fabianhartmann2/Deployment-Tower/exports/step/coupon_wifi_dock_v2.step

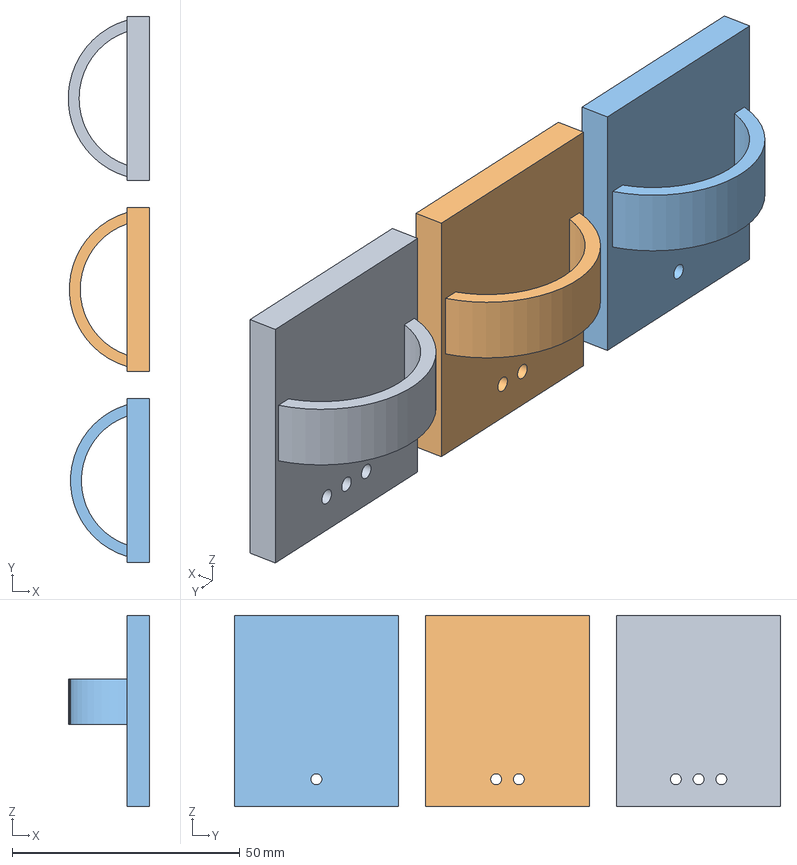
[picture p18: CAD file, 2026-10-05]
exports/step/coupon_wifi_dock_v2.step
17.9 x 120.0 x 42.0 mm
