fabianhartmann2/Deployment-Tower/exports/step/compliant_pad_template.step

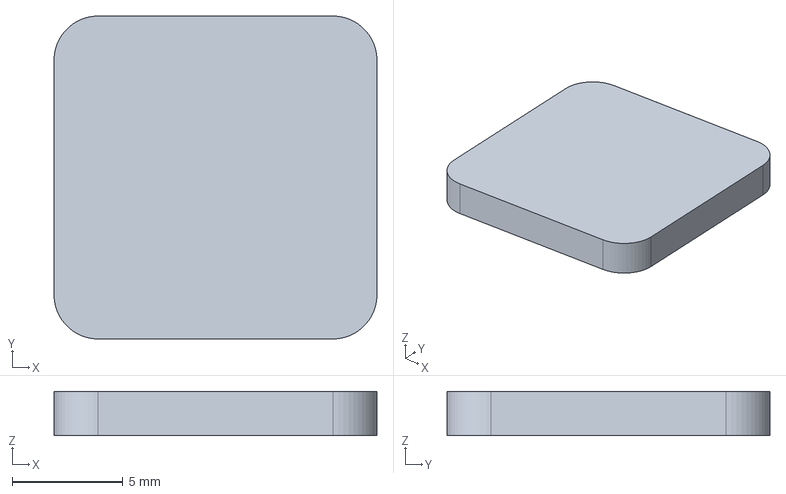
[picture p19: CAD file, 2026-10-05]
exports/step/compliant_pad_template.step
14.6 x 14.6 x 2.00 mm
