fabianhartmann2/Deployment-Tower/exports/step/coupon_rear_panel_fit_v2.step

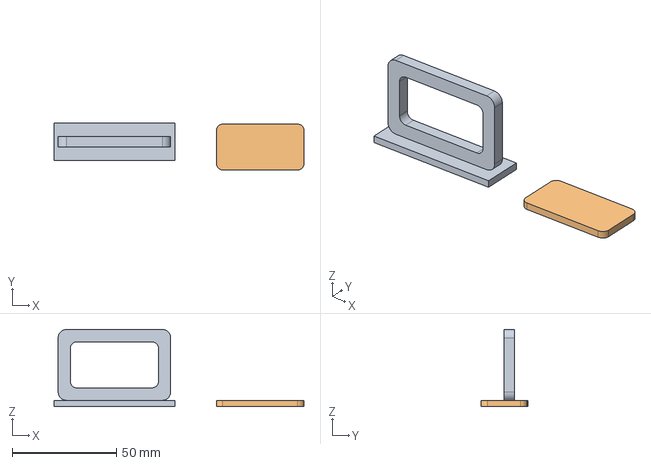
[picture p20: CAD file, 2026-10-05]
exports/step/coupon_rear_panel_fit_v2.step
120.0 x 22.5 x 37.0 mm
