fabianhartmann2/Deployment-Tower/exports/step/coupon_rear_io_v1.step

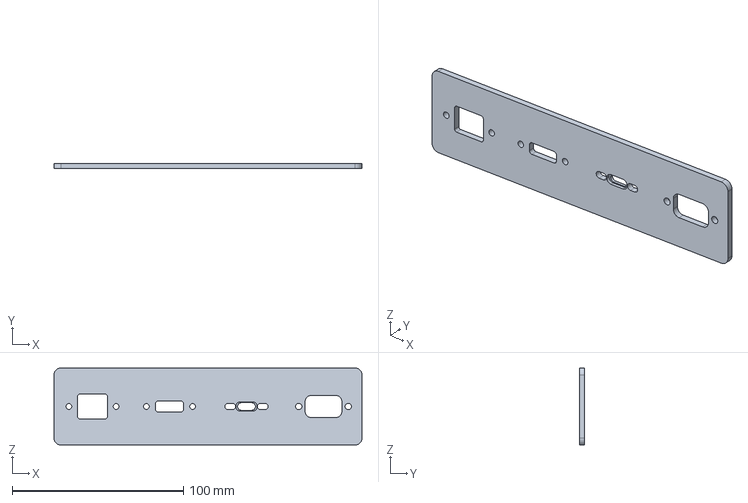
[picture p21: CAD file, 2026-10-05]
exports/step/coupon_rear_io_v1.step
180.0 x 3.20 x 45.0 mm
