fabianhartmann2/Deployment-Tower/exports/step/logo_panel_example_embossed.step

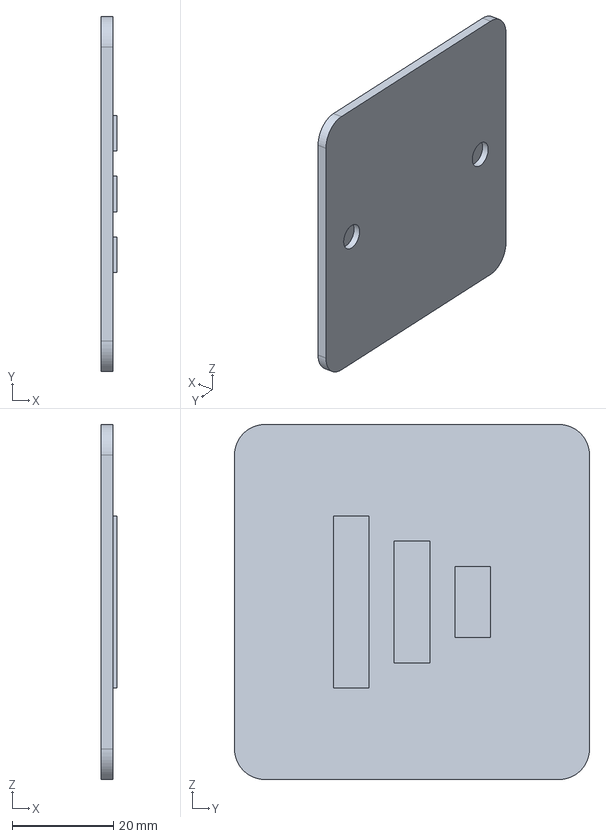
[picture p22: CAD file, 2026-10-05]
exports/step/logo_panel_example_embossed.step
3.20 x 70.0 x 70.0 mm
