fabianhartmann2/Deployment-Tower/exports/step/coupon_logo_mount.step

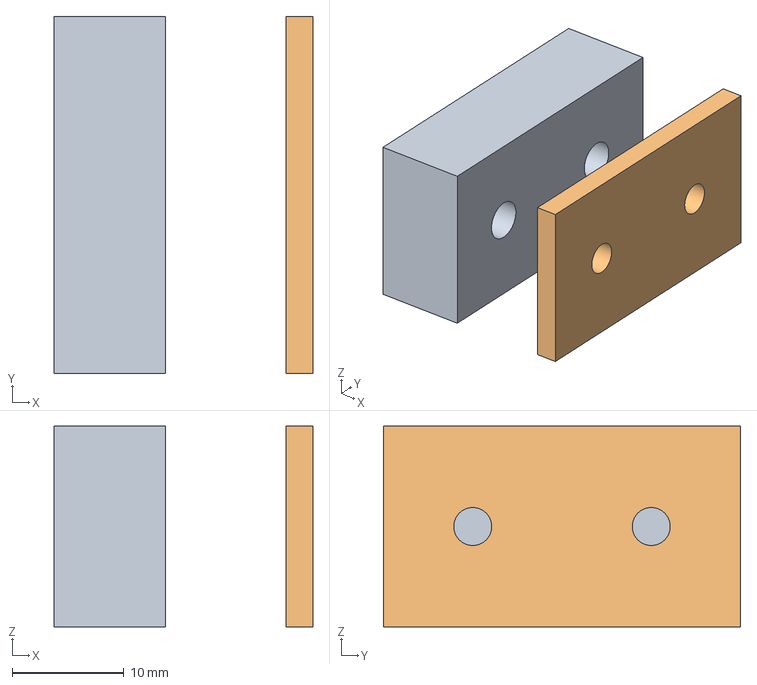
[picture p23: CAD file, 2026-10-05]
exports/step/coupon_logo_mount.step
23.2 x 32.0 x 18.0 mm
