fabianhartmann2/Deployment-Tower/exports/step/power_compartment_cover.step

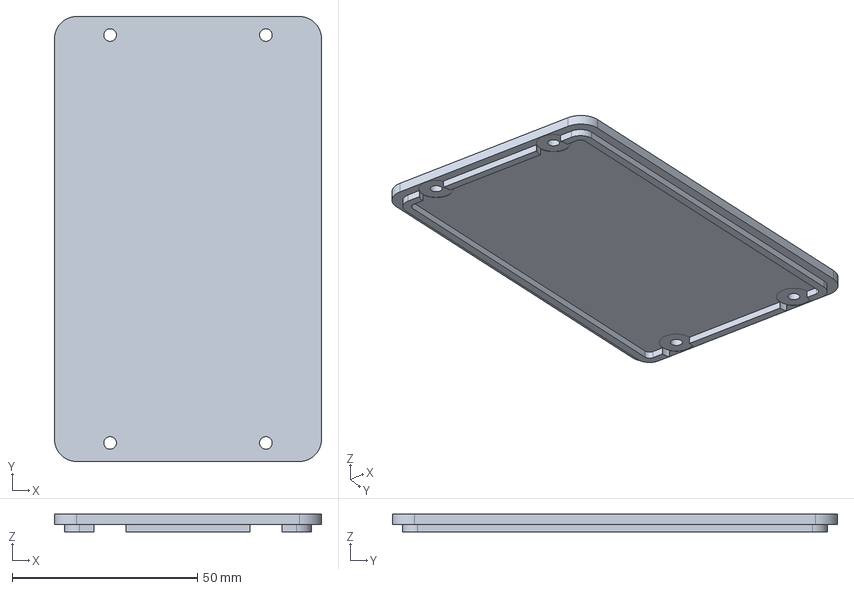
[picture p24: CAD file, 2026-10-05]
exports/step/power_compartment_cover.step
72.0 x 120.0 x 4.80 mm
