fabianhartmann2/Deployment-Tower/exports/step/lower_shell.step

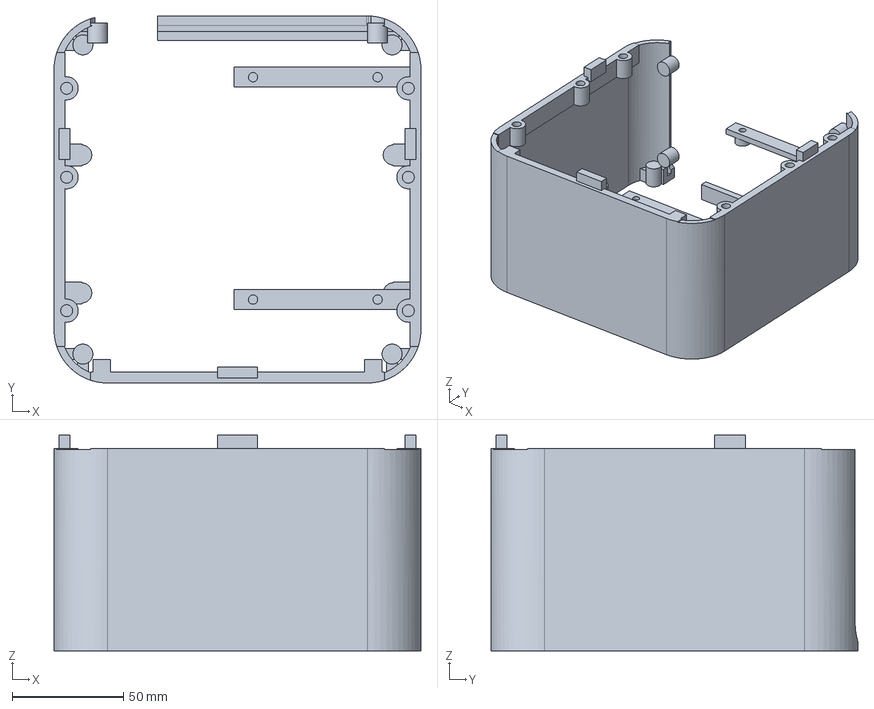
[picture p25: CAD file, 2026-10-05]
exports/step/lower_shell.step
165.0 x 165.0 x 97.0 mm
