fabianhartmann2/Deployment-Tower/exports/step/upper_cap.step

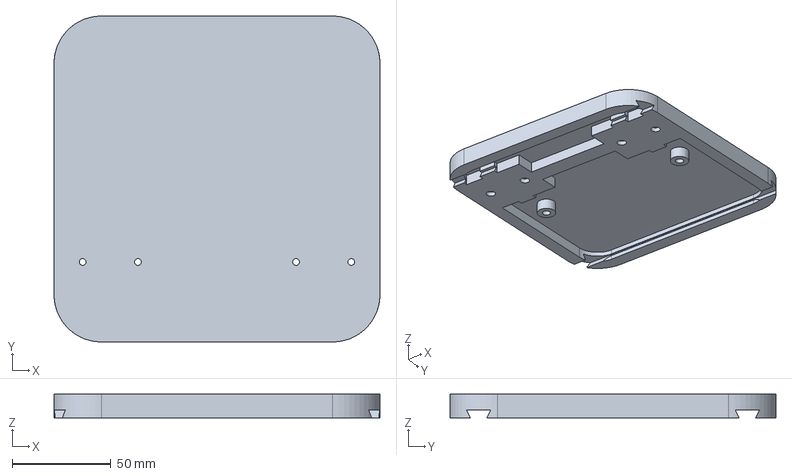
[picture p26: CAD file, 2026-10-05]
exports/step/upper_cap.step
165.0 x 165.0 x 12.0 mm
