fabianhartmann2/Deployment-Tower/exports/step/coupon_router_rf_access.step

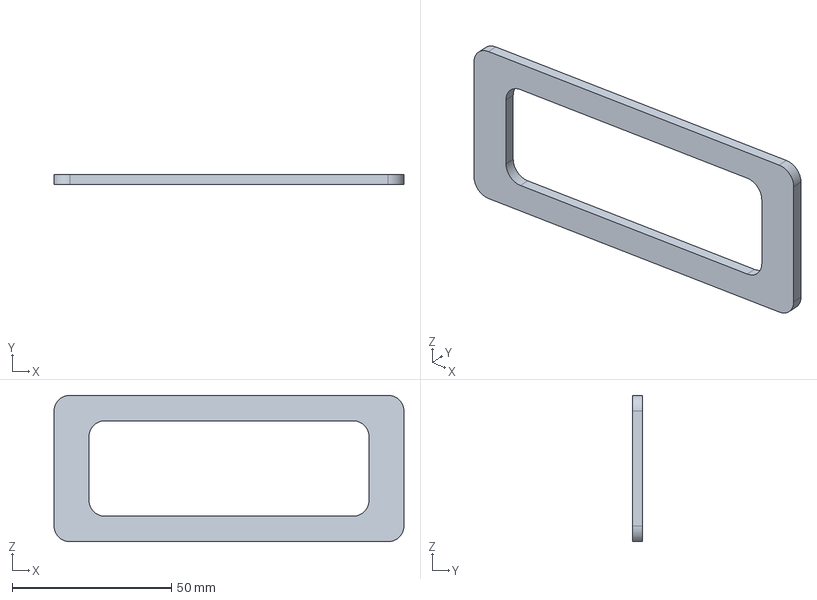
[picture p27: CAD file, 2026-10-05]
exports/step/coupon_router_rf_access.step
110.0 x 3.20 x 46.0 mm
