fabianhartmann2/Deployment-Tower/exports/step/coupon_rf_bulkhead_v1.step

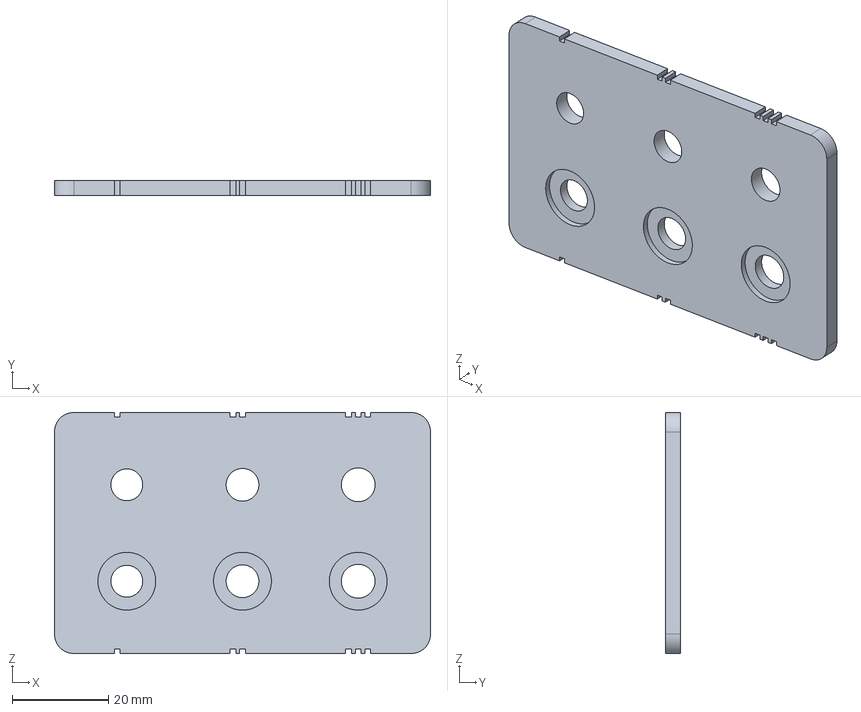
[picture p28: CAD file, 2026-10-05]
exports/step/coupon_rf_bulkhead_v1.step
78.0 x 3.20 x 50.0 mm
