fabianhartmann2/Deployment-Tower/exports/step/router_tray.step

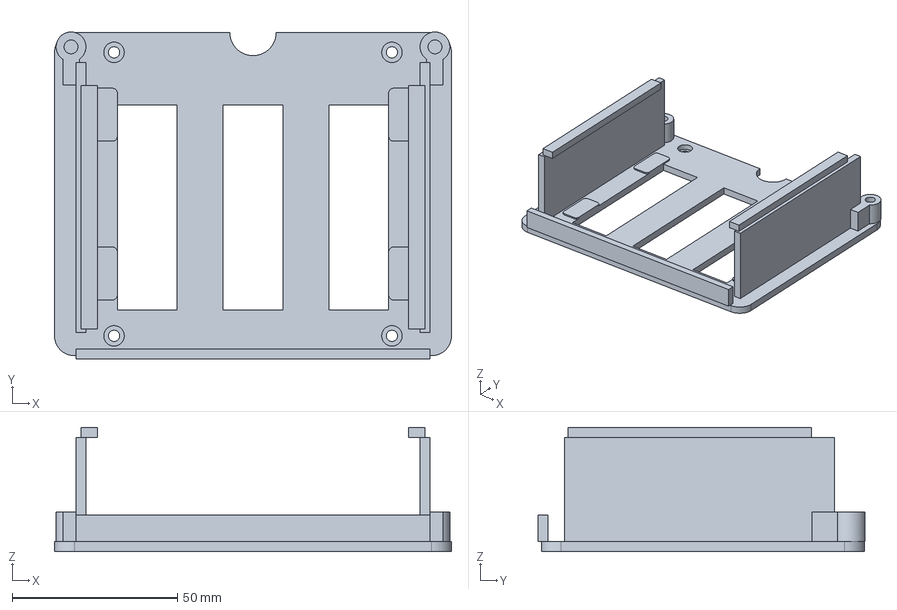
[picture p29: CAD file, 2026-10-05]
exports/step/router_tray.step
120.0 x 98.8 x 37.5 mm
