fabianhartmann2/Deployment-Tower/exports/step/coupon_c8_cutout.step

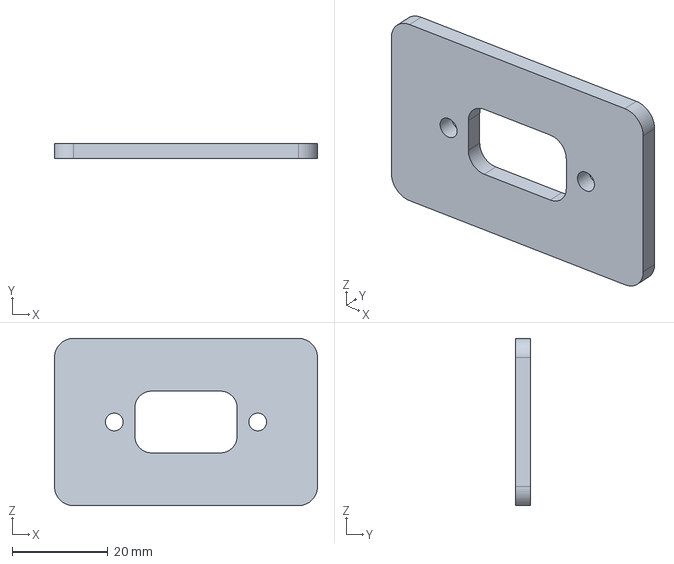
[picture p30: CAD file, 2026-10-05]
exports/step/coupon_c8_cutout.step
55.0 x 3.20 x 35.0 mm
