fabianhartmann2/Deployment-Tower/exports/step/base.step

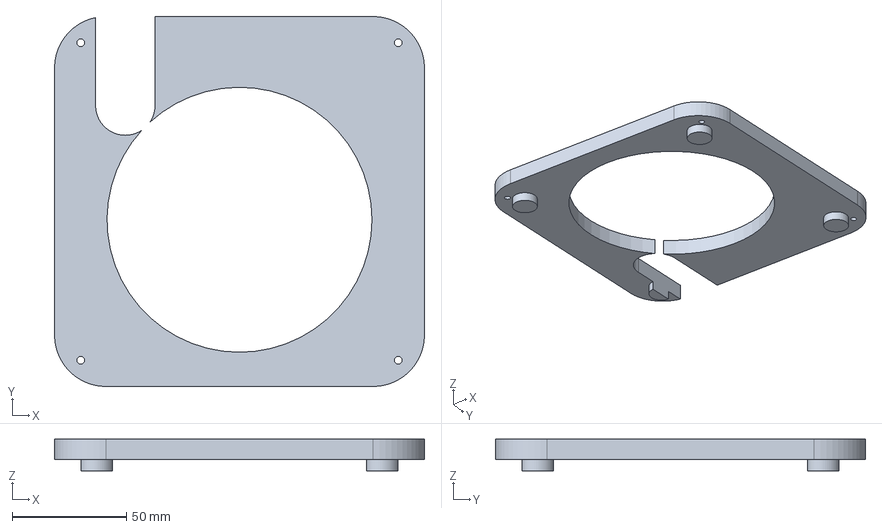
[picture p31: CAD file, 2026-10-05]
exports/step/base.step
162.0 x 162.0 x 14.0 mm
