fabianhartmann2/Deployment-Tower/exports/step/coupon_insert_boss.step

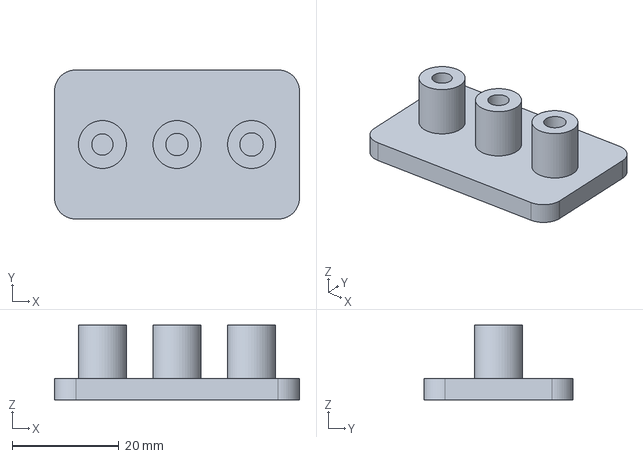
[picture p32: CAD file, 2026-10-05]
exports/step/coupon_insert_boss.step
46.0 x 28.0 x 14.0 mm
