fabianhartmann2/Deployment-Tower/exports/step/removable_handle.step

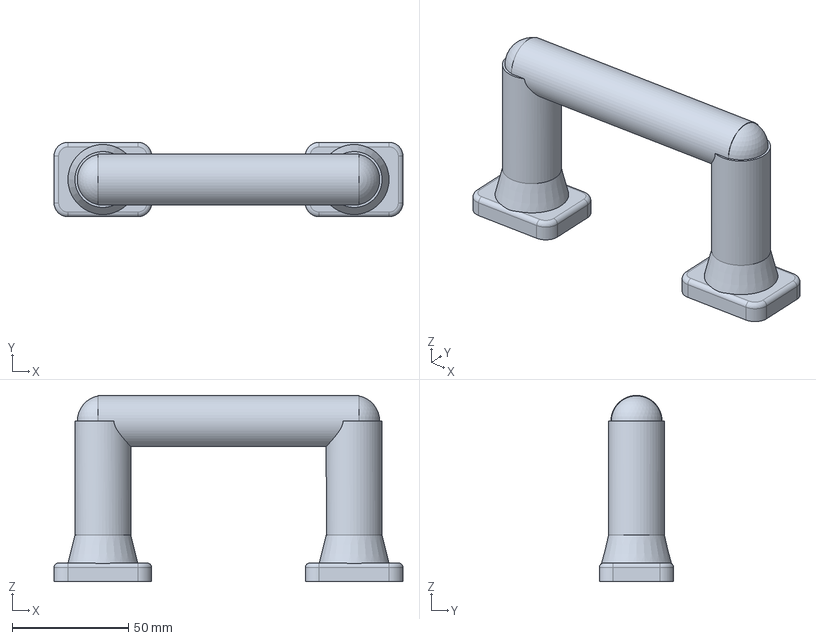
[picture p33: CAD file, 2026-10-05]
exports/step/removable_handle.step
150.0 x 32.0 x 80.0 mm
