fabianhartmann2/Deployment-Tower/exports/step/upper_shell.step

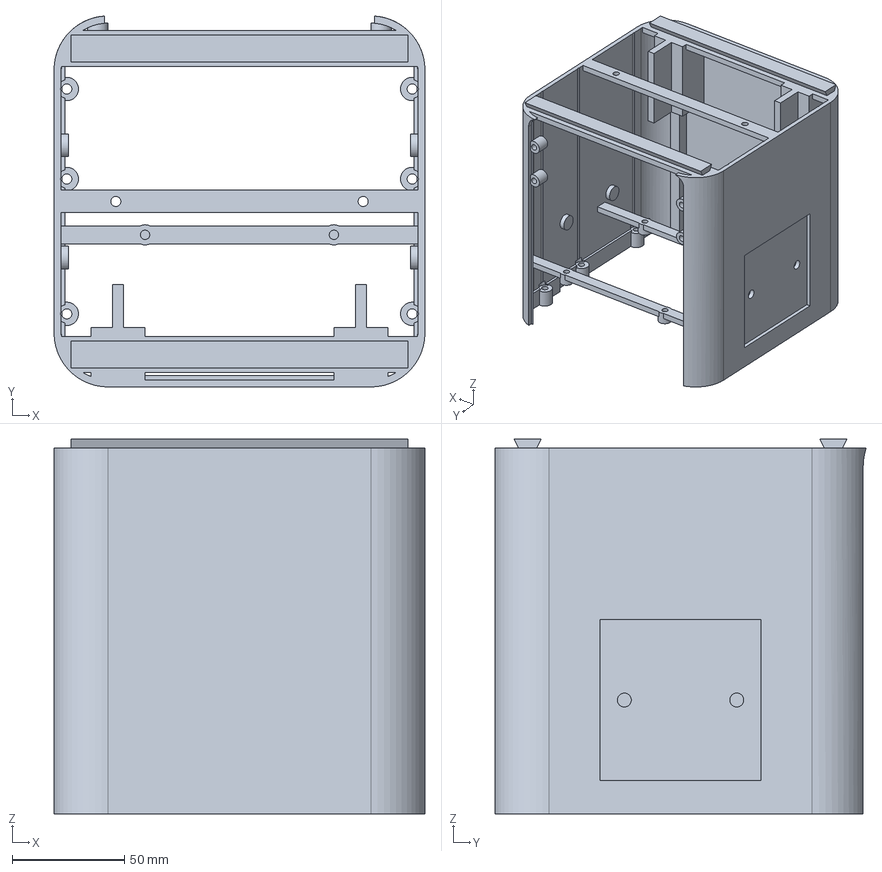
[picture p34: CAD file, 2026-10-05]
exports/step/upper_shell.step
165.0 x 165.0 x 166.6 mm
